konikoni428/ai_refrigerator/spresense/Spresense_AI_Refrigerator/config.h

/*
 *  config.h - WiFi Configration Header
 *
 *  This work is free software; you can redistribute it and/or modify it under the terms
 *  of the GNU Lesser General Public License as published by the Free Software Foundation;
 *  either version 2.1 of the License, or (at your option) any later version.
 *
 *  This work is distributed in the hope that it will be useful, but without any warranty;
 *  without even the implied warranty of merchantability or fitness for a particular
 *  purpose. See the GNU Lesser General Public License for more details.
 *
 *  You should have received a copy of the GNU Lesser General Public License along with
 *  this work; if not, write to the Free Software Foundation,
 *  Inc., 59 Temple Place, Suite 330, Boston, MA 02111-1307 USA
*/

#ifndef _CONFIG_H_
#define _CONFIG_H_

/*-------------------------------------------------------------------------*
 * Configration
 *-------------------------------------------------------------------------*/
#define  AP_SSID        "your-ssid"
#define  PASSPHRASE     "your-password"

#define  HTTP_SRVR_IP  "ai-refrigerator.konikoni428.com"
#define  HTTP_PORT     "80"
#define  HTTP_GET_PATH "/"
#define  HTTP_POST_PATH "/api/upload"
#define  HTTP_AUTH_KEY  "Bearer <YOUR API KEY>"

// #define ROOTCA_FILE    "ISRG_Root_X1.crt"

#endif /*_CONFIG_H_*/
